rryske2001/weather-station/software/internal-module-podwojne_bufor/main/logo.h

#pragma once
#include <stdint.h>

// Ustaw tutaj wymiary swojego obrazka (takie jak zrobiłeś w Paincie)
#define LOGO_WIDTH  100
#define LOGO_HEIGHT 100

static const uint16_t image_data_logo_pp_100px[10000] = {
   
    0xFFFF, 0xFFFF, 0xFFFF, 0xFFFF, 0xFFFF, 0xFFFF, 0xFFFF, 0xFFFF, 0xFFFF, 0xFFFF, 0xFFFF, 0xFFFF, 0xFFFF, 0xFFFF, 0xFFFF, 0xFFFF, 0xFFFF, 0xFFFF, 0xFFFF, 0xFFFF, 0xFFFF, 0xFFFF, 0xFFFF, 0xFFFF, 0xFFFF, 0xFFFF, 0xFFFF, 0xFFFF, 0xFFFF, 0xFFFF, 0xFFFF, 0xFFFF, 0xFFFF, 0xFFFF, 0xFFFF, 0xFFFF, 0xFFFF, 0xFFFF, 0xFFFF, 0xFFFF, 0x3103, 0x1103, 0x1103, 0x1103, 0x1103, 0x1103, 0x1103, 0x1103, 0x1103, 0x1103, 0x1103, 0x1103, 0x1103, 0x1103, 0x1103, 0x1103, 0x1103, 0x1103, 0x1103, 0x3103, 0xFFFF, 0xFFFF, 0xFFFF, 0xFFFF, 0xFFFF, 0xFFFF, 0xFFFF, 0xFFFF, 0xFFFF, 0xFFFF, 0xFFFF, 0xFFFF, 0xFFFF, 0xFFFF, 0xFFFF, 0xFFFF, 0xFFFF, 0xFFFF, 0xFFFF, 0xFFFF, 0xFFFF, 0xFFFF, 0xFFFF, 0xFFFF, 0xFFFF, 0xFFFF, 0xFFFF, 0xFFFF, 0xFFFF, 0xFFFF, 0xFFFF, 0xFFFF, 0xFFFF, 0xFFFF, 0xFFFF, 0xFFFF, 0xFFFF, 0xFFFF, 0xFFFF, 0xFFFF, 
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
    0xFFFF, 0x1103, 0x3203, 0xFFFF, 0xFFFF, 0xFFFF, 0xFFFF, 0xFFFF, 0xFFFF, 0xFFFF, 0xFFFF, 0xFFFF, 0xFFFF, 0xFFFF, 0xFFFF, 0x1103, 0x1103, 0xFFFF, 0xFFFF, 0xFFFF, 0xFFFF, 0xFFFF, 0xFFFF, 0xFFFF, 0xFFFF, 0xFFFF, 0xFFFF, 0xFFFF, 0xFFFF, 0xFFFF, 0xFFFF, 0x1103, 0x1103, 0xFFFF, 0xFFFF, 0xFFFF, 0xFFFF, 0x1103, 0x1103, 0x1103, 0x1103, 0xFFFF, 0xFFFF, 0xFFFF, 0x1103, 0x1103, 0x1103, 0x1103, 0xFFFF, 0x1103, 0x1103, 0x1103, 0x1103, 0x1103, 0x1103, 0xFFFF, 0xFFFF, 0xFFFF, 0xf102, 0x1103, 0x1103, 0x3103, 0xFFFF, 0xFFFF, 0xFFFF, 0xFFFF, 0xFFFF, 0x1103, 0x1103, 0xFFFF, 0xFFFF, 0xFFFF, 0xFFFF, 0xFFFF, 0xFFFF, 0xFFFF, 0xFFFF, 0xFFFF, 0xFFFF, 0xFFFF, 0xFFFF, 0xFFFF, 0xFFFF, 0x1103, 0x1103, 0xFFFF, 0xFFFF, 0xFFFF, 0xFFFF, 0xFFFF, 0xFFFF, 0xFFFF, 0xFFFF, 0xFFFF, 0xFFFF, 0xFFFF, 0xFFFF, 0x3103, 0x1103, 0xFFFF, 
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
};
