rryske2001/weather-station/software/internal-module-podwojne_bufor/main/wifi_project.c

#include <string.h>
#include "freertos/FreeRTOS.h"
#include "freertos/task.h"
#include "freertos/event_groups.h"
#include "esp_system.h"
#include "esp_wifi.h"
#include "esp_event.h"
#include "esp_log.h"
#include "nvs_flash.h"
#include "wifi_project.h"

static const char *TAG = "WIFI_MODULE";

// Grupa zdarzeń do synchronizacji (żebyśmy mogli poczekać na połączenie)
static EventGroupHandle_t s_wifi_event_group;
#define WIFI_CONNECTED_BIT BIT0
#define WIFI_FAIL_BIT      BIT1

static int s_retry_num = 0;
#define MAX_RETRY 5

// --- OBSŁUGA ZDARZEŃ (TO JEST "MÓZG" WIFI) ---
static void event_handler(void* arg, esp_event_base_t event_base,
                                int32_t event_id, void* event_data)
{
    // 1. WiFi wystartowało -> Próbujemy się połączyć
    if (event_base == WIFI_EVENT && event_id == WIFI_EVENT_STA_START) {
        esp_wifi_connect();
    } 
    // 2. Połączenie zerwane lub nieudane -> Próbujemy ponownie
    else if (event_base == WIFI_EVENT && event_id == WIFI_EVENT_STA_DISCONNECTED) {
        if (s_retry_num < MAX_RETRY) {
            esp_wifi_connect();
            s_retry_num++;
            ESP_LOGI(TAG, "Ponawiam próbe połączenia z AP...");
        } else {
            // Poddajemy się po 5 próbach
            xEventGroupSetBits(s_wifi_event_group, WIFI_FAIL_BIT);
        }
        ESP_LOGI(TAG,"Nie udalo sie polaczyc z AP");
    } 
    // 3. Sukces! Dostaliśmy adres IP (to oznacza pełne połączenie)
    else if (event_base == IP_EVENT && event_id == IP_EVENT_STA_GOT_IP) {
        ip_event_got_ip_t* event = (ip_event_got_ip_t*) event_data;
        ESP_LOGI(TAG, "Uzyskano IP: " IPSTR, IP2STR(&event->ip_info.ip));
        s_retry_num = 0;
        // Ustawiamy flagę sukcesu, żeby funkcja główna przestała czekać
        xEventGroupSetBits(s_wifi_event_group, WIFI_CONNECTED_BIT);
    }
}

int wifi_connect_station(const char *ssid, const char *password)
{
    // 1. Tworzymy grupę zdarzeń
    s_wifi_event_group = xEventGroupCreate();

    // 2. Inicjalizacja warstwy sieciowej (Netif)
    ESP_ERROR_CHECK(esp_netif_init());

    // 3. Tworzymy domyślną pętlę zdarzeń systemowych
    ESP_ERROR_CHECK(esp_event_loop_create_default());
    esp_netif_create_default_wifi_sta();

    // 4. Domyślna konfiguracja WiFi
    wifi_init_config_t cfg = WIFI_INIT_CONFIG_DEFAULT();
    ESP_ERROR_CHECK(esp_wifi_init(&cfg));

    // 5. Rejestracja funkcji 'event_handler' do nasłuchiwania zdarzeń
    esp_event_handler_instance_t instance_any_id;
    esp_event_handler_instance_t instance_got_ip;
    ESP_ERROR_CHECK(esp_event_handler_instance_register(WIFI_EVENT,
                                                        ESP_EVENT_ANY_ID,
                                                        &event_handler,
                                                        NULL,
                                                        &instance_any_id));
    ESP_ERROR_CHECK(esp_event_handler_instance_register(IP_EVENT,
                                                        IP_EVENT_STA_GOT_IP,
                                                        &event_handler,
                                                        NULL,
                                                        &instance_got_ip));

    // 6. Ustawienie SSID i Hasła
    wifi_config_t wifi_config = {
        .sta = {
            .threshold.authmode = WIFI_AUTH_WPA2_PSK, // Wymagane WPA2 (bezpieczeństwo)
            .pmf_cfg = {
                .capable = true,
                .required = false
            },
        },
    };
    // Kopiujemy bezpiecznie stringi do struktury (bo struktura ma tablice o stałej długości)
    strlcpy((char*)wifi_config.sta.ssid, ssid, sizeof(wifi_config.sta.ssid));
    strlcpy((char*)wifi_config.sta.password, password, sizeof(wifi_config.sta.password));

    // 7. Wgranie konfiguracji
    ESP_ERROR_CHECK(esp_wifi_set_mode(WIFI_MODE_STA) ); // Tryb Station (Klient)
    ESP_ERROR_CHECK(esp_wifi_set_config(WIFI_IF_STA, &wifi_config) );
    
    // 8. START!
    ESP_ERROR_CHECK(esp_wifi_start() );

    ESP_LOGI(TAG, "Oczekiwanie na polaczenie...");

    // 9. Czekanie na wynik (blokujemy program w tym miejscu aż dostaniemy IP lub Błąd)
    EventBits_t bits = xEventGroupWaitBits(s_wifi_event_group,
            WIFI_CONNECTED_BIT | WIFI_FAIL_BIT,
            pdFALSE,
            pdFALSE,
            portMAX_DELAY);

    // 10. Analiza wyniku
    if (bits & WIFI_CONNECTED_BIT) {
        ESP_LOGI(TAG, "Polaczono z SSID: %s", ssid);
        return 1;
    } else if (bits & WIFI_FAIL_BIT) {
        ESP_LOGI(TAG, "Blad polaczenia z SSID: %s", ssid);
        return 0;
    } else {
        ESP_LOGE(TAG, "Nieoczekiwane zdarzenie");
        return 0;
    }
}
